akira345/Discrete-FM-Radio-Receiver-Project/Docs/FM_IF_5V/figures/ad3.png

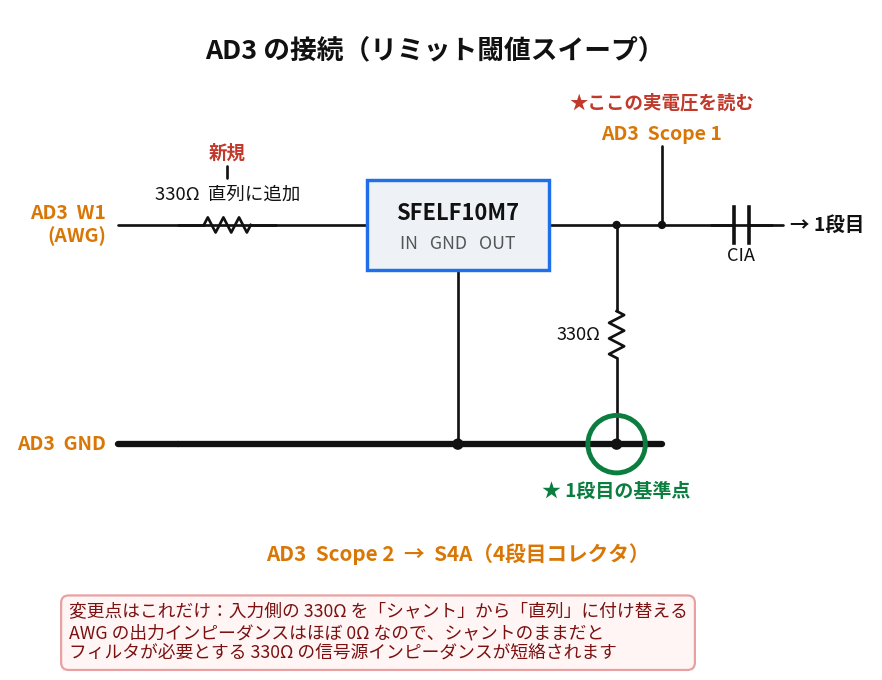
Docs/FM_IF_5V/figures/ad3.png
