akira345/Discrete-FM-Radio-Receiver-Project/Docs/FM_IF_5V/figures/chk_bias.png

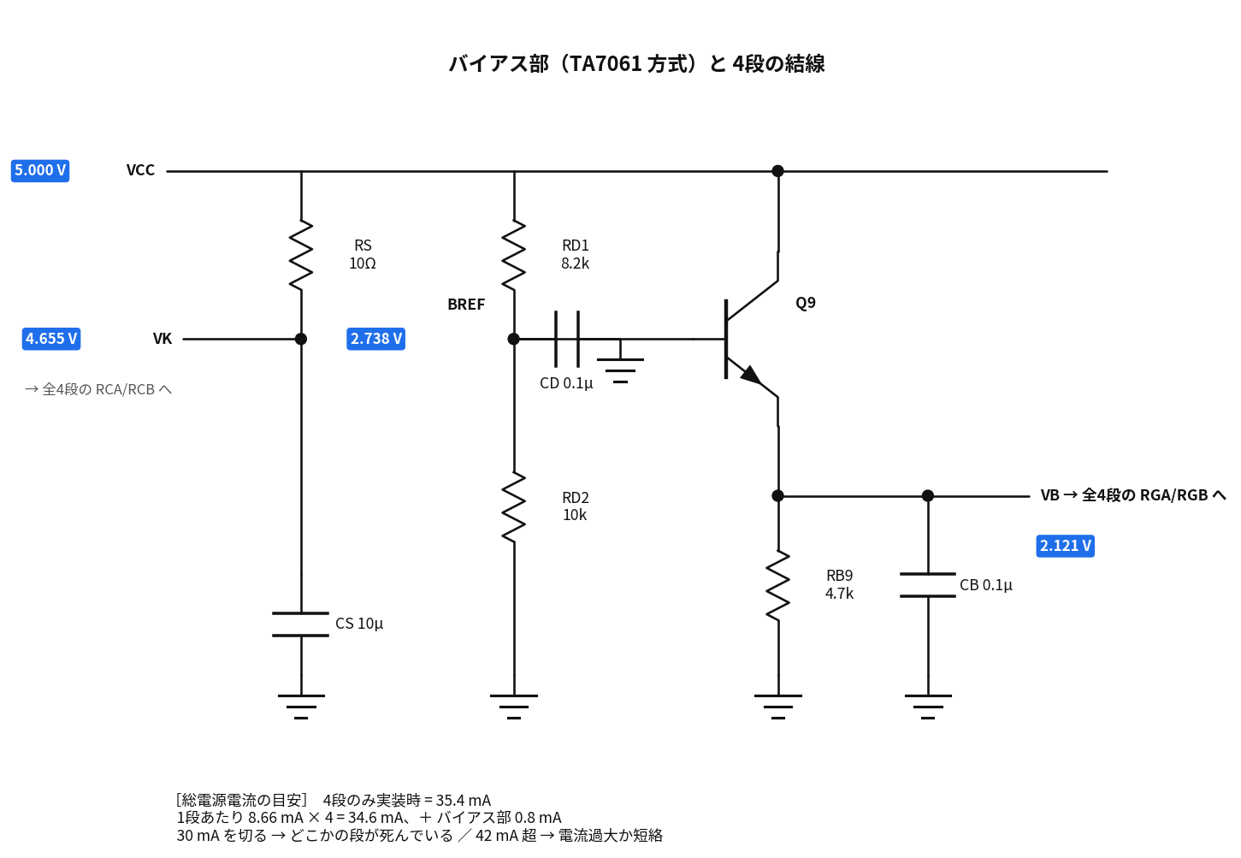
Docs/FM_IF_5V/figures/chk_bias.png
