akira345/Discrete-FM-Radio-Receiver-Project/Docs/FM_IF_5V/figures/gainshape.png

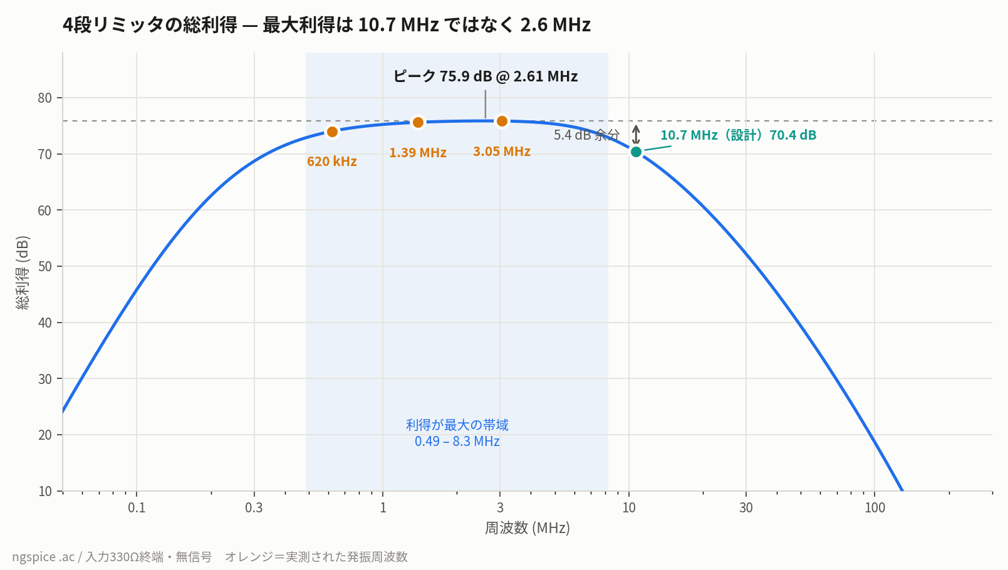
Docs/FM_IF_5V/figures/gainshape.png
