akira345/Discrete-FM-Radio-Receiver-Project/Docs/FM_IF_5V/figures/gndpath.png

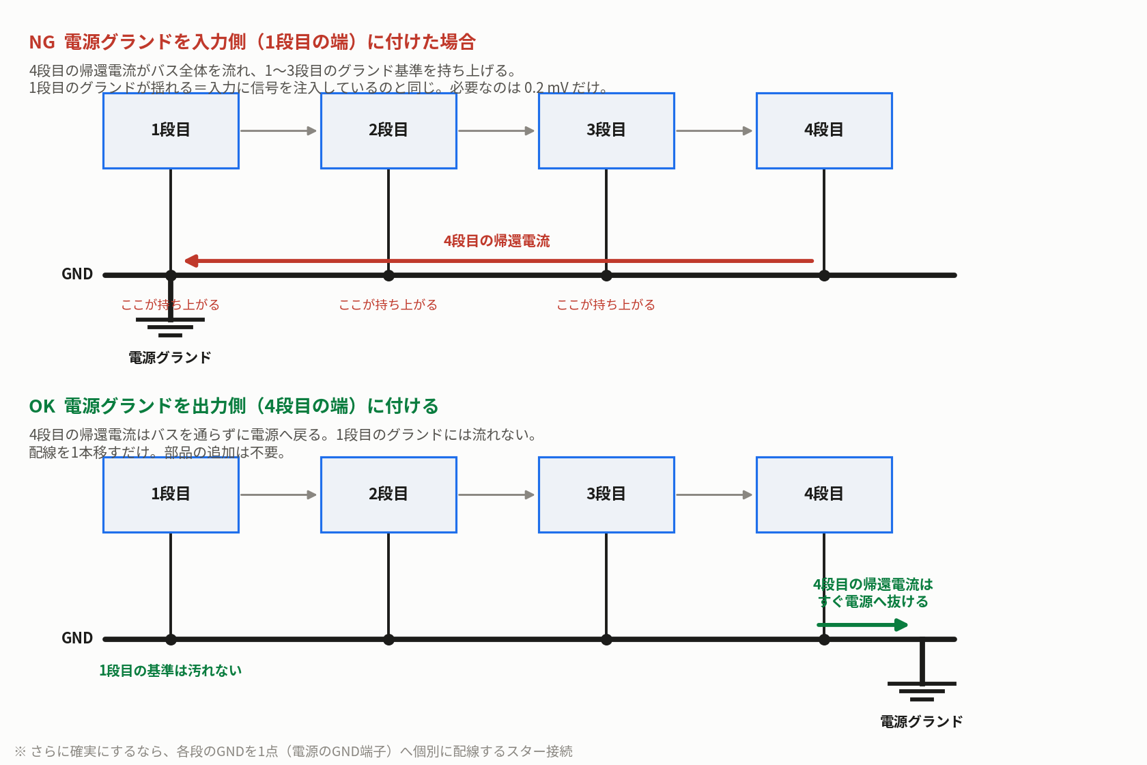
Docs/FM_IF_5V/figures/gndpath.png
