akira345/Discrete-FM-Radio-Receiver-Project/Docs/FM_IF_5V/figures/mpx_sync_block.png

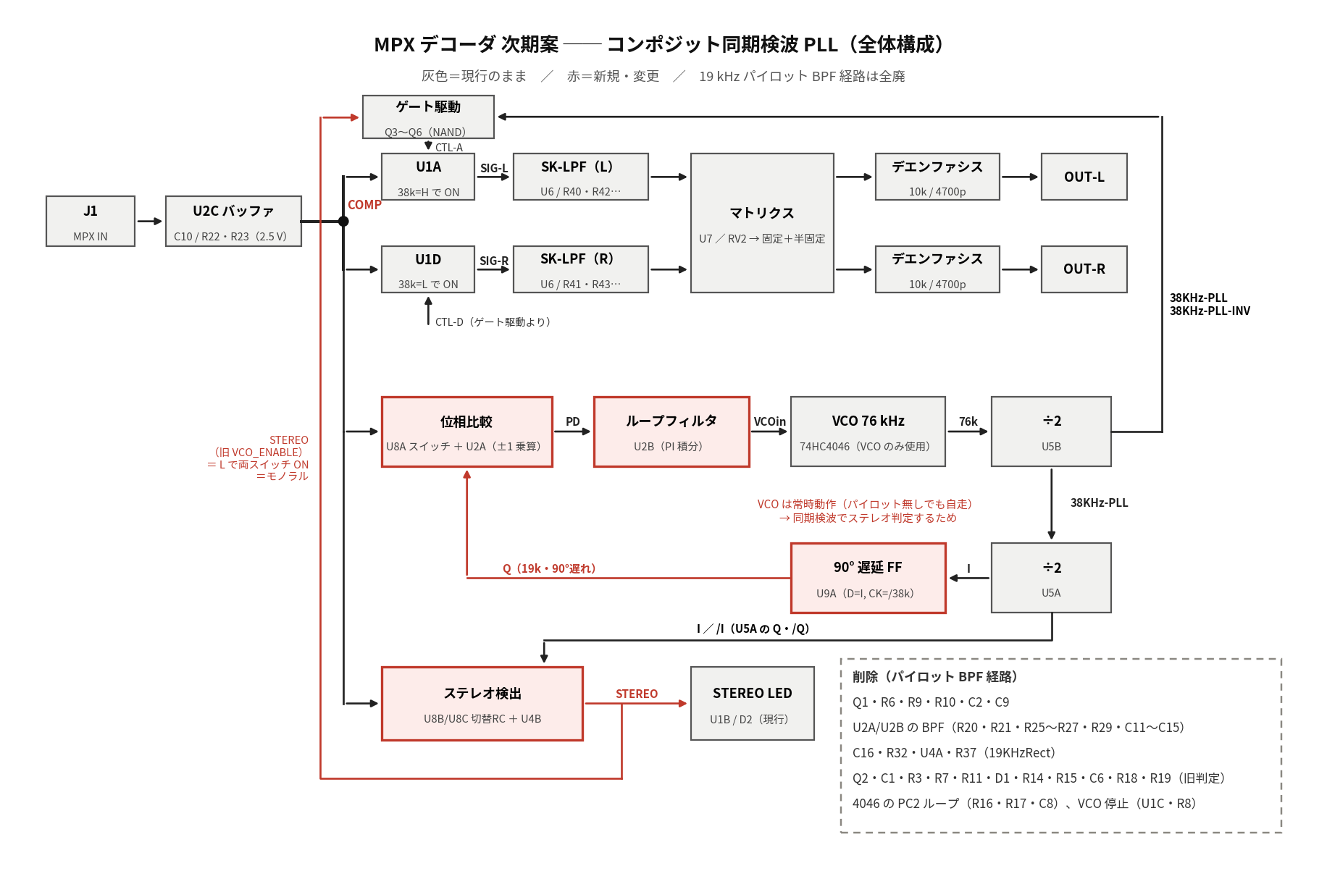
Docs/FM_IF_5V/figures/mpx_sync_block.png
