akira345/Discrete-FM-Radio-Receiver-Project/Docs/FM_IF_5V/figures/scurve.png

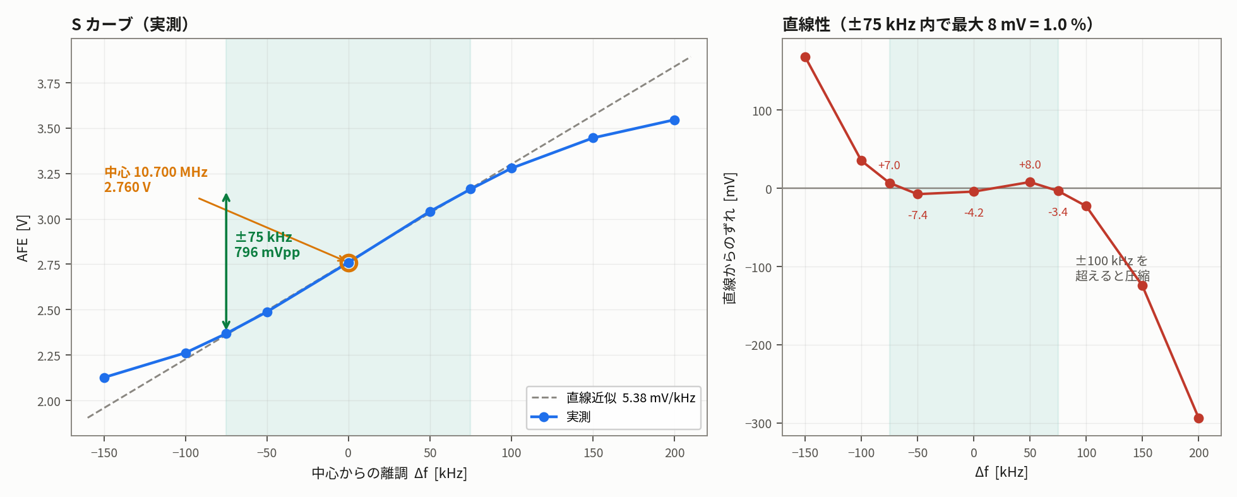
Docs/FM_IF_5V/figures/scurve.png
