akira345/Discrete-FM-Radio-Receiver-Project/Docs/FM_IF_5V/figures/sys_final.png

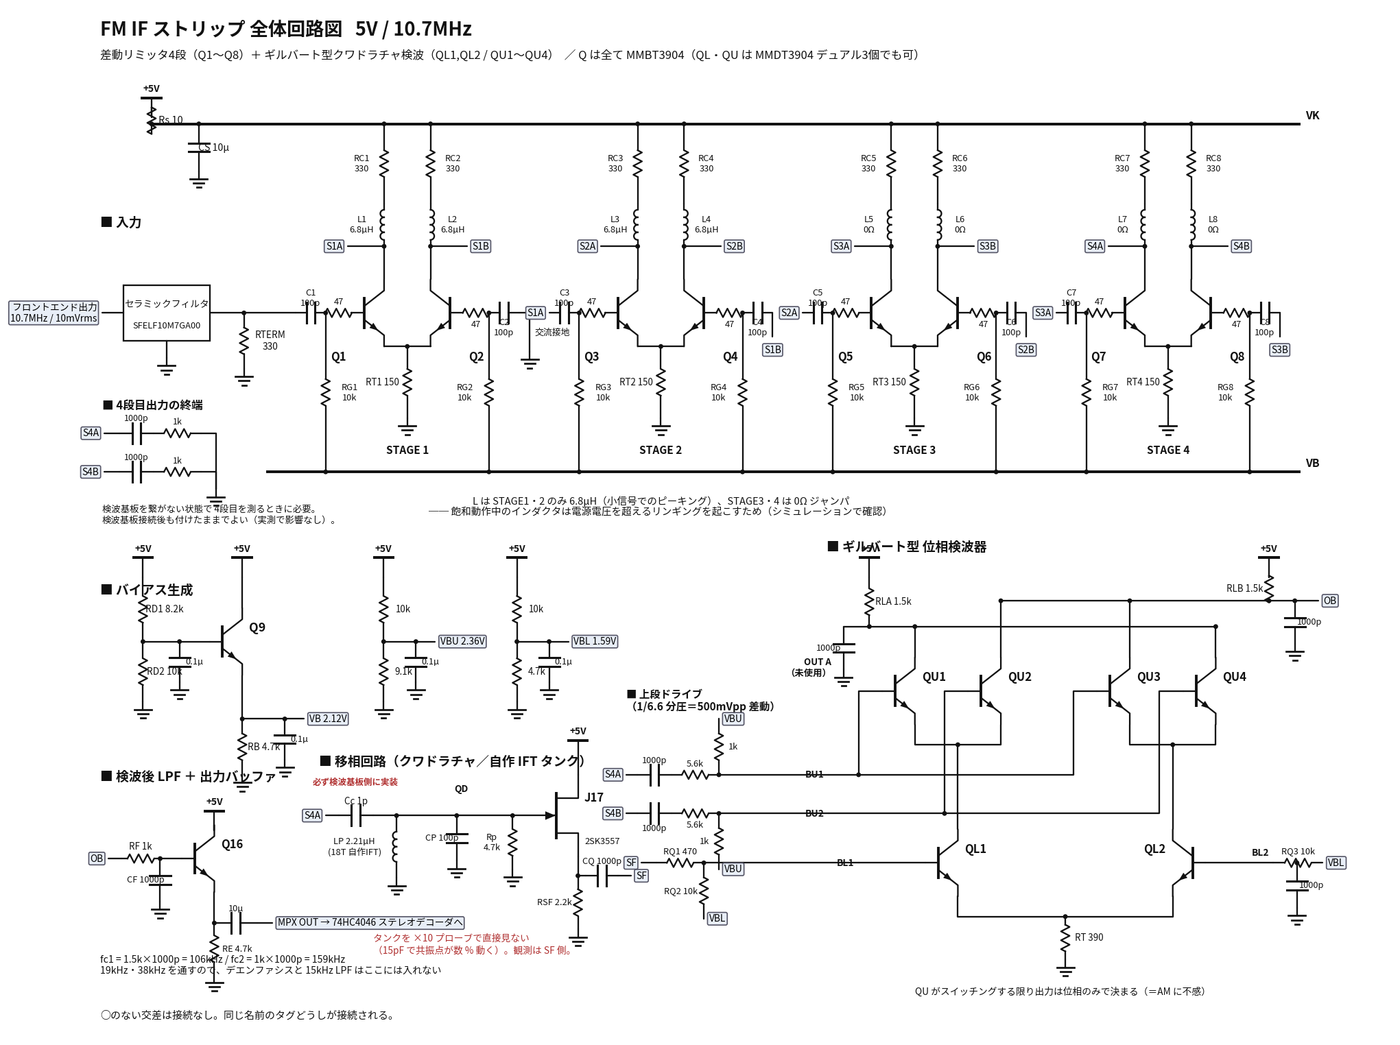
Docs/FM_IF_5V/figures/sys_final.png
