akira345/Discrete-FM-Radio-Receiver-Project/Docs/FM_IF_5V/reference/det_board.png

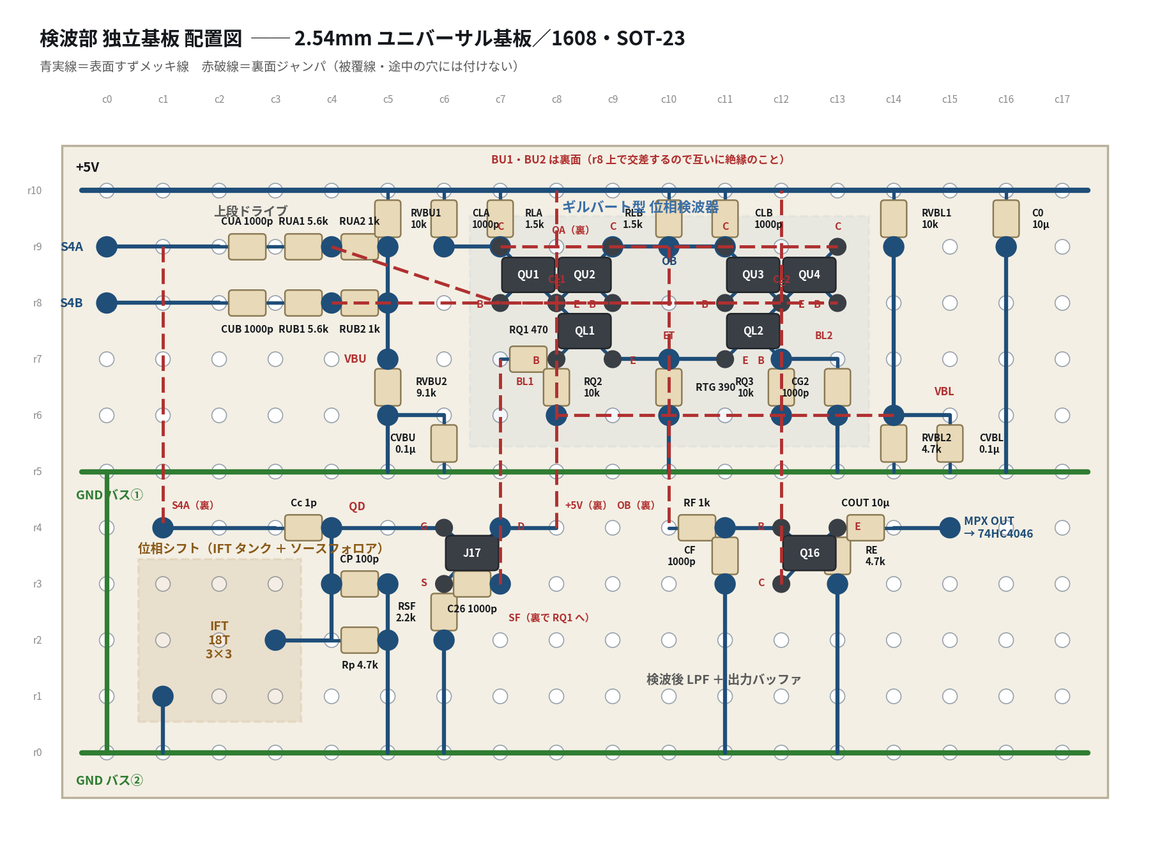
Docs/FM_IF_5V/reference/det_board.png
