akira345/Discrete-FM-Radio-Receiver-Project/Docs/FM_IF_5V/test_signals/mpx_L1k_check.png

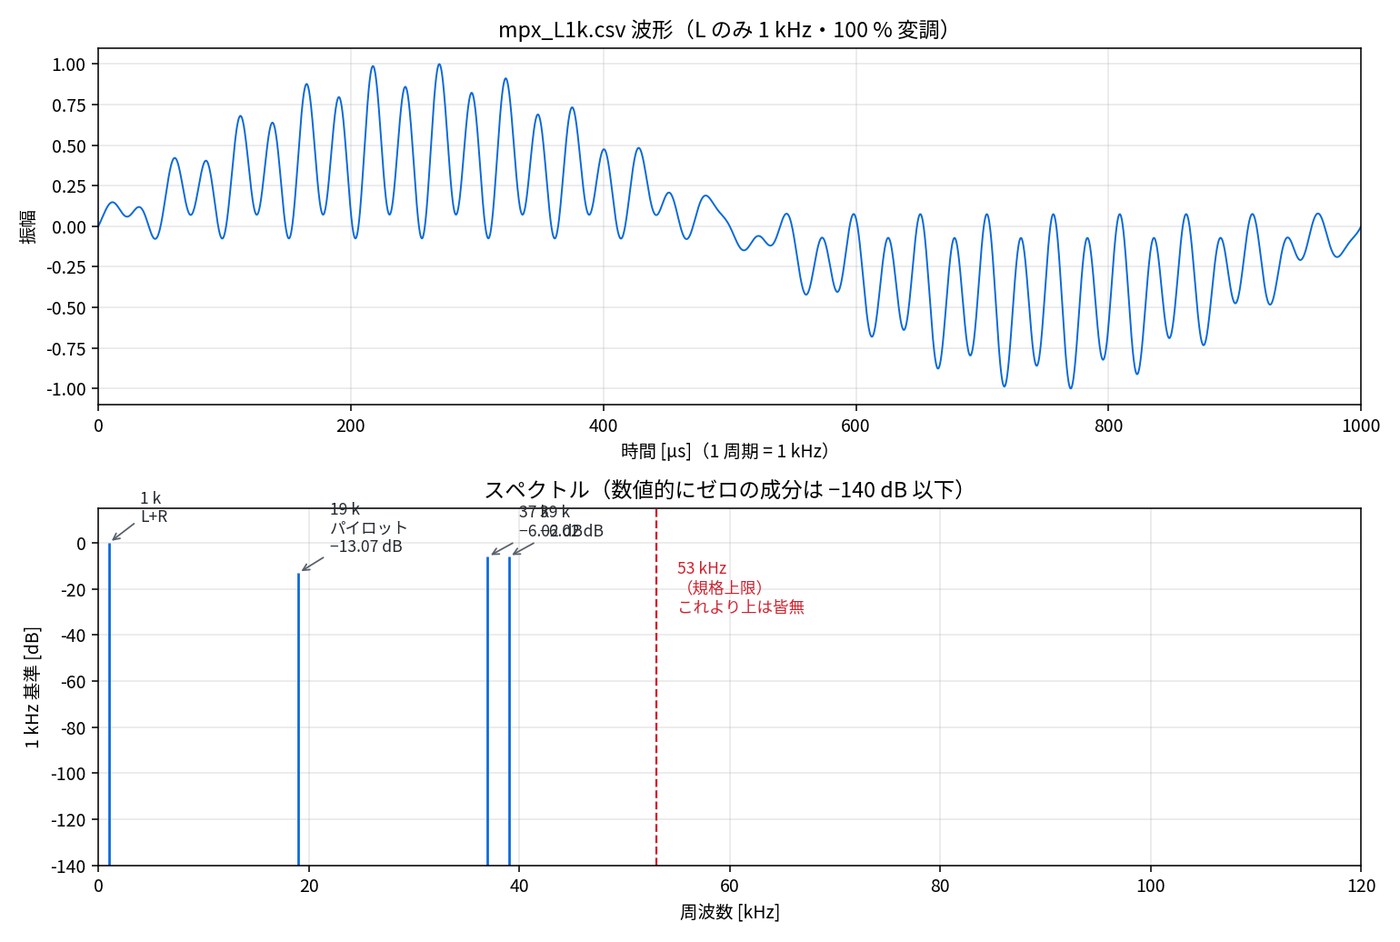
Docs/FM_IF_5V/test_signals/mpx_L1k_check.png
