akira345/Discrete-FM-Radio-Receiver-Project/Docs/FM_IF_5V/test_signals/preview_check.png

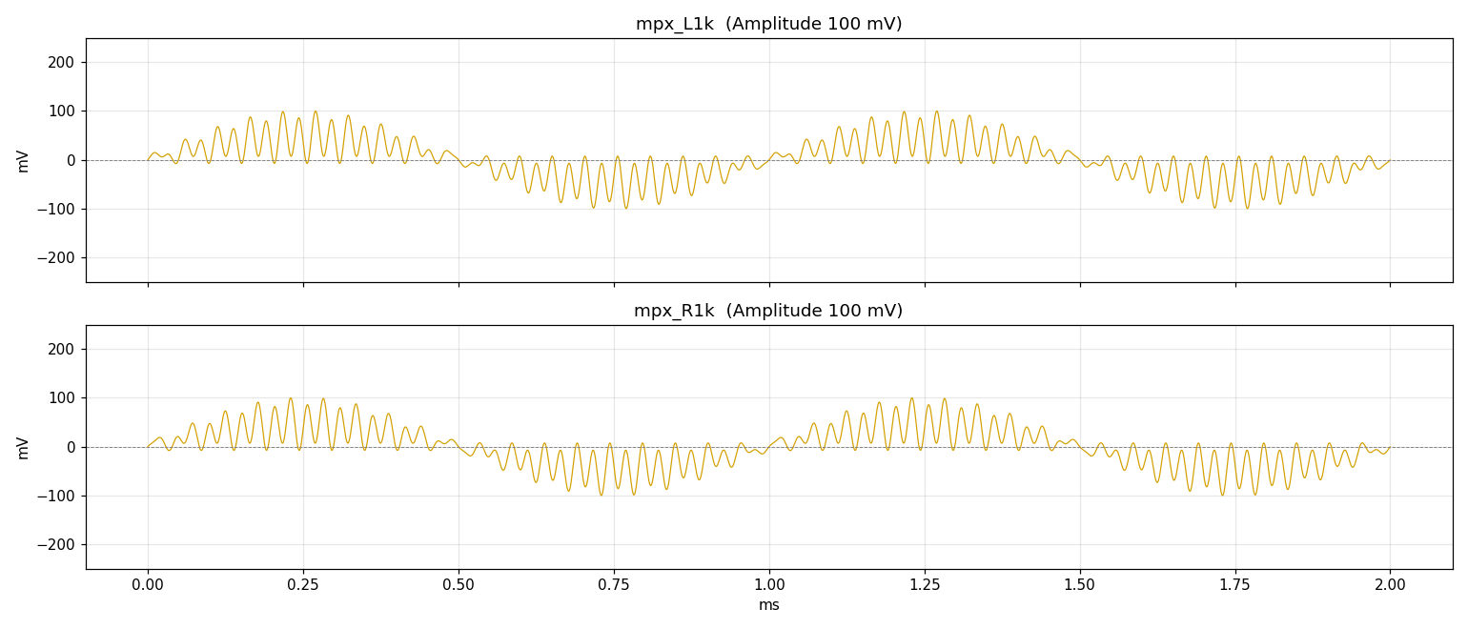
Docs/FM_IF_5V/test_signals/preview_check.png
