akira345/Discrete-FM-Radio-Receiver-Project/MPXDecorder-V4_SMD/MPXDecorder-V4_SMD.kicad_pcb

## KiCad design MPXDecorder-V4_SMD/MPXDecorder-V4_SMD.kicad_pcb (2026-10-10)

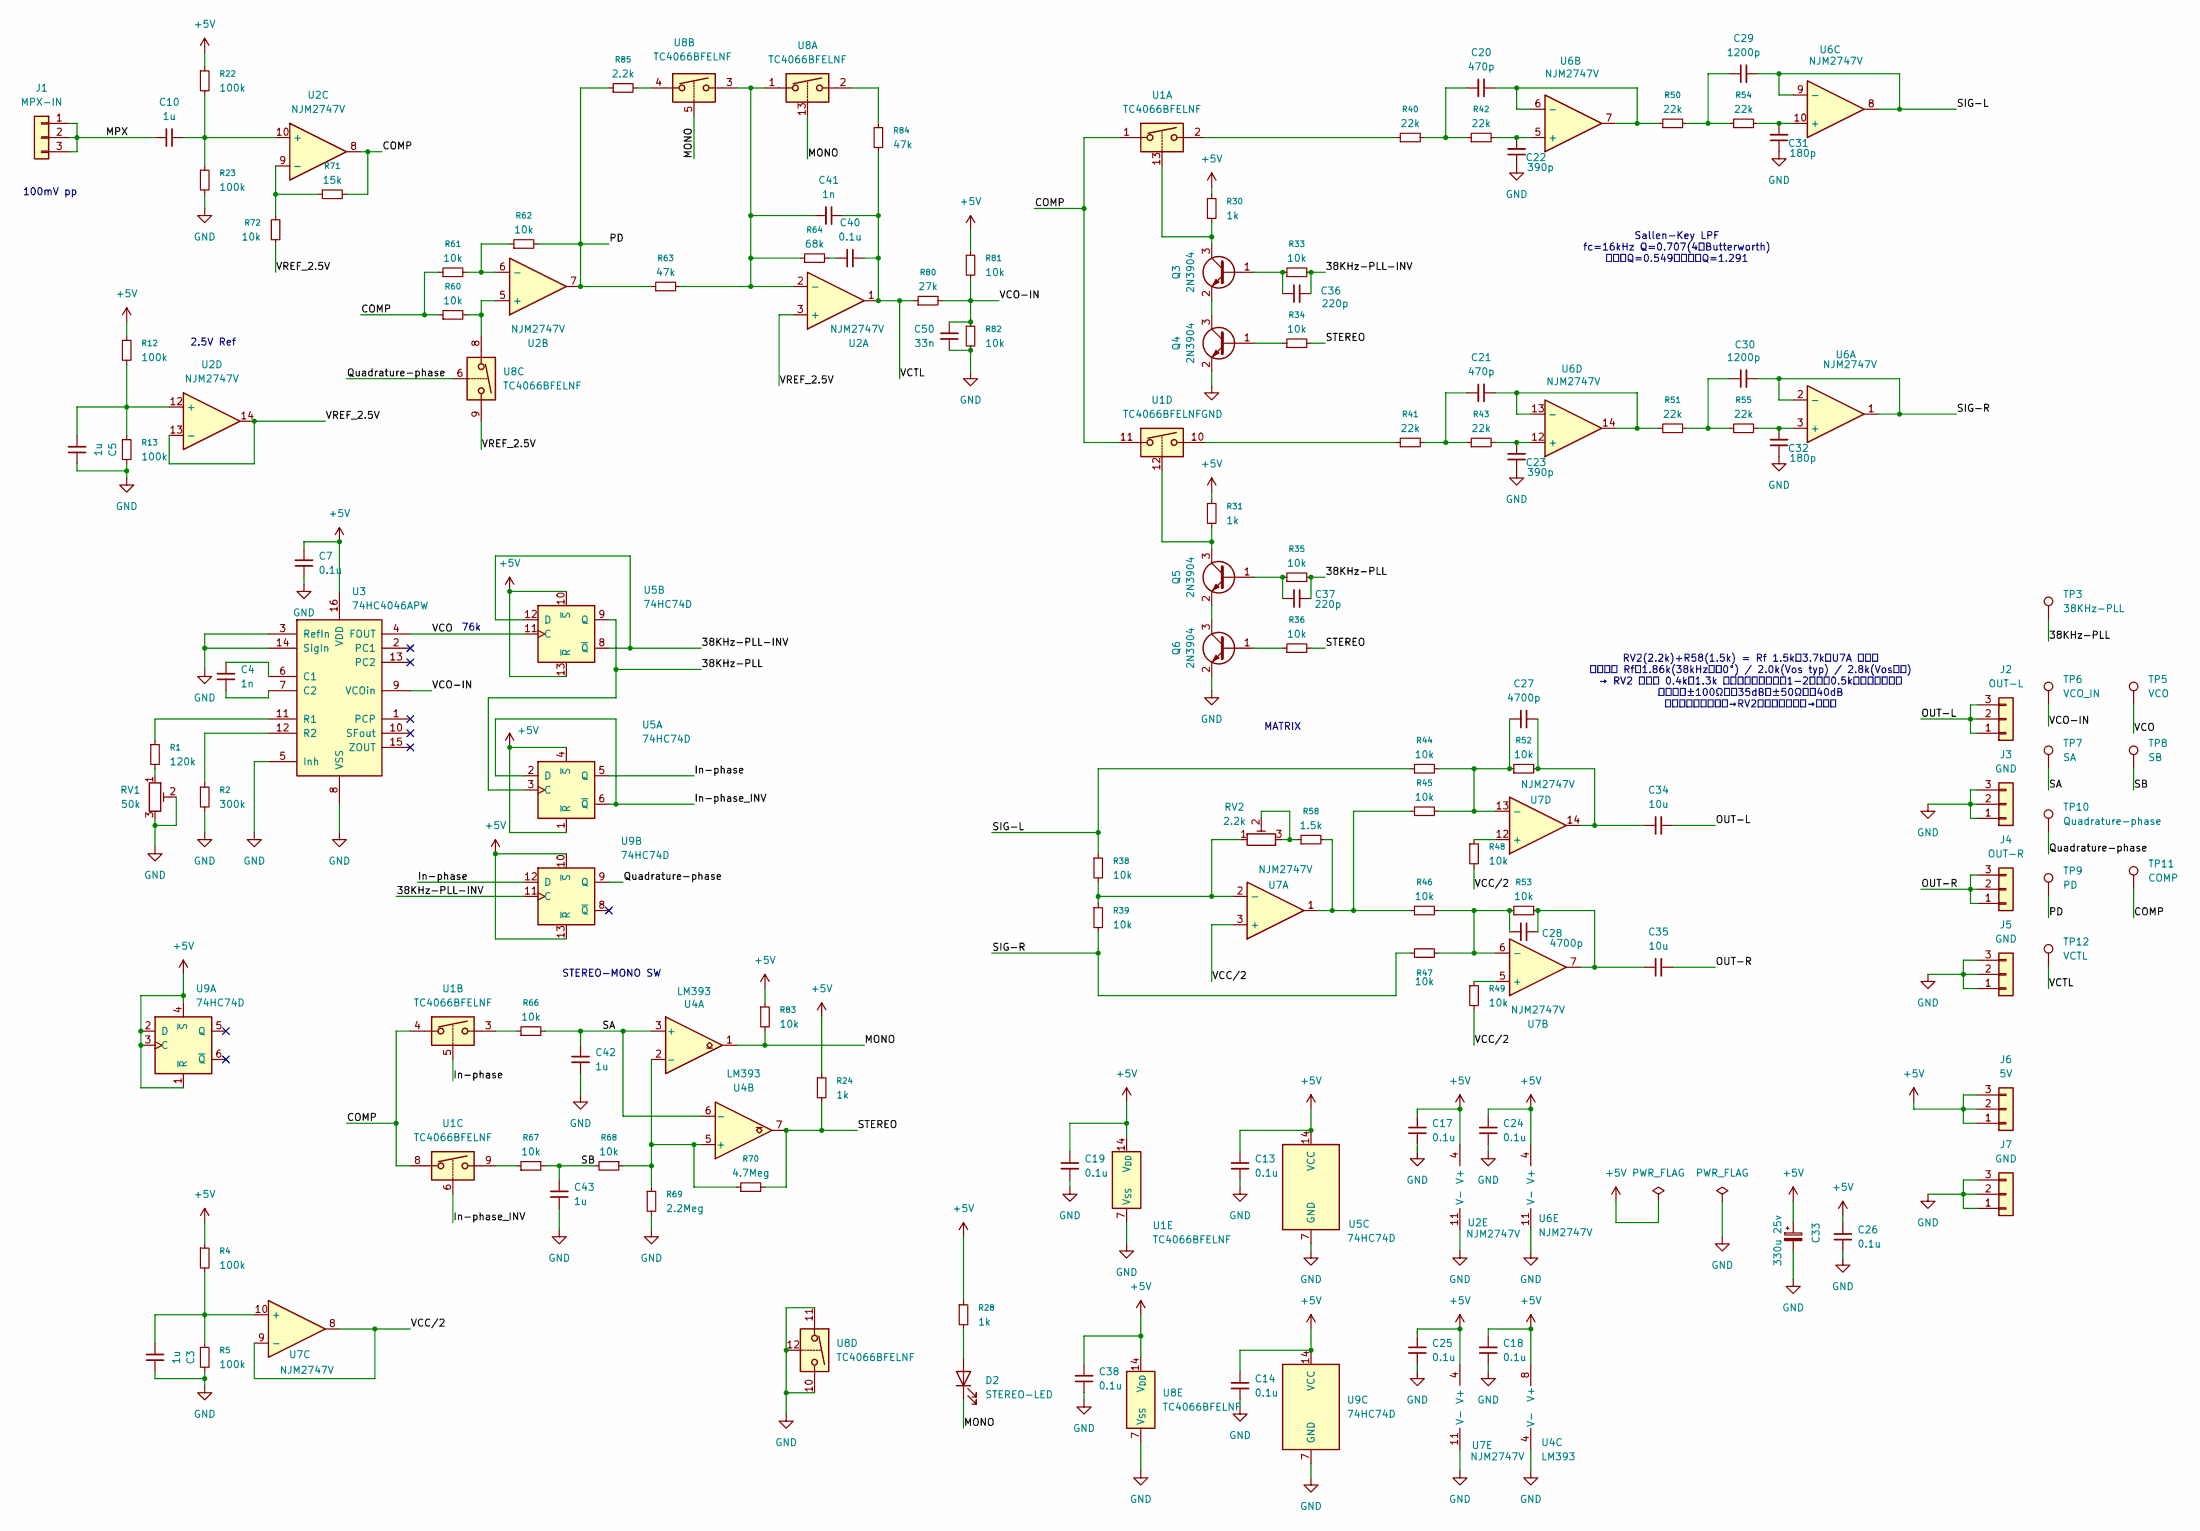
[picture p19: schematic MPXDecorder-V4_SMD.kicad_sch, FM MPX Decorder]

Parts:
C3, C5, C10, C42, C43: 1u; C_0603_1608Metric_Pad1.08x0.95mm_HandSolder
C4: 1n; C_0603_1608Metric_Pad1.08x0.95mm_HandSolder
C7, C13, C14, C17, C18, C19, C24, C25, C26, C38, C40: 0.1u; C_0603_1608Metric_Pad1.08x0.95mm_HandSolder
C20, C21: 470p; C_0603_1608Metric_Pad1.08x0.95mm_HandSolder
C22, C23: 390p; C_0603_1608Metric_Pad1.08x0.95mm_HandSolder
C27, C28: 4700p; C_0603_1608Metric_Pad1.08x0.95mm_HandSolder
C29, C30: 1200p; C_0603_1608Metric_Pad1.08x0.95mm_HandSolder
C31, C32: 180p; C_0603_1608Metric_Pad1.08x0.95mm_HandSolder
C33: 330u 25v; CP_Elec_10x10
C34, C35: 10u; C_1206_3216Metric_Pad1.33x1.80mm_HandSolder
C36, C37: 220p; C_0603_1608Metric_Pad1.08x0.95mm_HandSolder
C41: 1n; C_0805_2012Metric_Pad1.18x1.45mm_HandSolder
C50: 33n; C_1206_3216Metric_Pad1.33x1.80mm_HandSolder
D2: STEREO-LED; LED_0603_1608Metric_Pad1.05x0.95mm_HandSolder
J1: MPX-IN; PinHeader_1x03_P2.54mm_Vertical
J2: OUT-L; PinHeader_1x03_P2.54mm_Vertical
J3, J5, J7: GND; PinHeader_1x03_P2.54mm_Vertical
J4: OUT-R; PinHeader_1x03_P2.54mm_Vertical
J6: 5V; PinHeader_1x03_P2.54mm_Vertical
Q3, Q4, Q5, Q6: 2N3904; SOT-23_Handsoldering
R1: 120k; R_0603_1608Metric_Pad0.98x0.95mm_HandSolder
R2: 300k; R_0603_1608Metric_Pad0.98x0.95mm_HandSolder
R4, R5, R12, R13, R22, R23: 100k; R_0603_1608Metric_Pad0.98x0.95mm_HandSolder
R24, R28, R30, R31: 1k; R_0603_1608Metric_Pad0.98x0.95mm_HandSolder
R33, R34, R35, R36, R38, R39, R44, R45, R46, R47, R48, R49, R52, R53, R60, R61, R62, R66, R67, R68, R72, R81, R82, R83: 10k; R_0603_1608Metric_Pad0.98x0.95mm_HandSolder
R40, R41, R42, R43, R50, R51, R54, R55: 22k; R_0603_1608Metric_Pad0.98x0.95mm_HandSolder
R58: 1.5k; R_0603_1608Metric_Pad0.98x0.95mm_HandSolder
R63, R84: 47k; R_0603_1608Metric_Pad0.98x0.95mm_HandSolder
R64: 68k; R_0603_1608Metric_Pad0.98x0.95mm_HandSolder
R69: 2.2Meg; R_0603_1608Metric_Pad0.98x0.95mm_HandSolder
R70: 4.7Meg; R_0603_1608Metric_Pad0.98x0.95mm_HandSolder
R71: 15k; R_0603_1608Metric_Pad0.98x0.95mm_HandSolder
R80: 27k; R_0603_1608Metric_Pad0.98x0.95mm_HandSolder
R85: 2.2k; R_0603_1608Metric_Pad0.98x0.95mm_HandSolder
RV1: 50k; Potentiometer_Bourns_TC33X_Vertical
RV2: 2.2k; Potentiometer_Bourns_TC33X_Vertical
TP3: 38KHz-PLL; TestPoint_Pad_2.5x2.5mm
TP5: VCO; TestPoint_Pad_2.5x2.5mm
TP6: VCO_IN; TestPoint_Pad_2.5x2.5mm
TP7: SA; TestPoint_Pad_2.5x2.5mm
TP8: SB; TestPoint_Pad_2.5x2.5mm
TP9: PD; TestPoint_Pad_2.5x2.5mm
TP10: Quadrature-phase; TestPoint_Pad_2.5x2.5mm
TP11: COMP; TestPoint_Pad_2.5x2.5mm
TP12: VCTL; TestPoint_Pad_2.5x2.5mm
U1, U8: TC4066BFELNF; SO-14_5.3x10.2mm_P1.27mm
U2, U6, U7: NJM2747V; SSOP-14_5.3x6.2mm_P0.65mm
U3: 74HC4046APW; TSSOP-16_4.4x5mm_P0.65mm
U4: LM393; SOIC-8_3.9x4.9mm_P1.27mm
U5, U9: 74HC74D; SOIC-14_3.9x8.7mm_P1.27mm

Connections:
+5V: C7.1, C13.1, C14.1, C17.1, C18.1, C19.1, C24.1, C25.1, C26.1, C33.1, C38.1, J6.1, J6.2, J6.3, R4.1, R12.1, R22.1, R24.1, R28.1, R30.1, R31.1, R81.1, R83.1, U1.14 (V_{DD}), U2.4 (V+), U3.16 (VDD), U4.8 (V+), U5.1 (~R), U5.4 (~S), U5.10 (~S), U5.13 (~R), U5.14 (VCC), U6.4 (V+), U7.4 (V+), U8.14 (V_{DD}), U9.1 (~R), U9.2 (D), U9.3 (C), U9.4 (~S), U9.10 (~S), U9.13 (~R), U9.14 (VCC)
/38KHz-PLL: C37.2, R35.2, TP3.1 (1_1), U5.3 (C), U5.9 (Q)
/38KHz-PLL-INV: C36.2, R33.2, U5.8 (~Q), U5.12 (D), U9.11 (C)
/COMP: R60.1, R61.1, R71.2, TP11.1 (1_1), U1.1, U1.4, U1.8, U1.11, U2.8
/In-phase: U1.5, U5.5 (Q), U9.12 (D)
/In-phase_INV: U1.6, U5.2 (D), U5.6 (~Q)
/MONO: D2.1 (K), R83.2, U4.1, U8.5, U8.13
/MPX: C10.1, J1.1, J1.2, J1.3
/OUT-L: C34.2, J2.1, J2.2, J2.3
/OUT-R: C35.2, J4.1, J4.2, J4.3
/PD: R62.2, R63.1, R85.1, TP9.1 (1_1), U2.7
/Quadrature-phase: TP10.1 (1_1), U8.6, U9.9 (Q)
/SA: C42.1, R66.2, TP7.1 (1_1), U4.3 (+), U4.6 (-)
/SB: C43.1, R67.2, R68.2, TP8.1 (1_1)
/SIG-L: C29.2, R38.1, R44.1, U6.8, U6.9 (-)
/SIG-R: C30.2, R39.2, R47.1, U6.1, U6.2 (-)
/STEREO: R24.2, R34.2, R36.2, R70.2, U4.7
/VCC/2: R48.2, R49.2, U7.3 (+), U7.8, U7.9 (-)
/VCO: TP5.1 (1_1), U3.4 (FOUT), U5.11 (C)
/VCO-IN: C50.1, R80.2, R81.2, R82.1, TP6.1 (1_1), U3.9 (VCOin)
/VCTL: C40.2, C41.2, R80.1, R84.1, TP12.1 (1_1), U2.1
/VREF_2.5V: R72.1, U2.3 (+), U2.13 (-), U2.14, U8.9
GND: C3.2, C5.2, C7.2, C13.2, C14.2, C17.2, C18.2, C19.2, C22.1, C23.1, C24.2, C25.2, C26.2, C31.1, C32.1, C33.2, C38.2, C42.2, C43.2, C50.2, J3.1, J3.2, J3.3, J5.1, J5.2, J5.3, J7.1, J7.2, J7.3, Q4.2 (E), Q6.2 (E), R2.2, R5.2, R13.2, R23.2, R69.2, R82.2, RV1.2, RV1.3, U1.7 (V_{SS}), U2.11 (V-), U3.3 (RefIn), U3.5 (Inh), U3.8 (VSS), U3.14 (SigIn), U4.4 (V-), U5.7 (GND), U6.11 (V-), U7.11 (V-), U8.7 (V_{SS}), U8.10, U8.11, U8.12, U9.7 (GND)
unnamed: C20.1, R40.2, R42.1
unnamed: C21.1, R41.2, R43.1
unnamed: C27.2, C34.1, R52.2, U7.14
unnamed: C28.2, C35.1, R53.2, U7.7
unnamed: C29.1, R50.2, R54.1
unnamed: C30.1, R51.2, R55.1
unnamed: C40.1, R64.2
unnamed: D2.2 (A), R28.2
unnamed: C36.1, Q3.1 (B), R33.1
unnamed: Q3.3 (C), R30.2, U1.13
unnamed: Q3.2 (E), Q4.3 (C)
unnamed: Q4.1 (B), R34.1
unnamed: C37.1, Q5.1 (B), R35.1
unnamed: Q5.3 (C), R31.2, U1.12
unnamed: Q5.2 (E), Q6.3 (C)
unnamed: Q6.1 (B), R36.1
unnamed: R1.2, RV1.1
unnamed: R40.1, U1.2
unnamed: R41.1, U1.10
unnamed: R45.1, R46.1, R58.2, U7.1
unnamed: R58.1, RV2.2, RV2.3
unnamed: R66.1, U1.3
unnamed: R67.1, U1.9
unnamed: R84.2, U8.2
unnamed: R85.2, U8.4
unnamed: C41.1, R63.2, R64.1, U2.2 (-), U8.1, U8.3
unnamed: R60.2, U2.5 (+), U8.8
unnamed: R61.2, R62.1, U2.6 (-)
unnamed: C10.2, R22.2, R23.1, U2.10 (+)
unnamed: R71.1, R72.2, U2.9 (-)
unnamed: C5.1, R12.2, R13.1, U2.12 (+)
unnamed: C4.1, U3.6 (C1)
unnamed: C4.2, U3.7 (C2)
unnamed: R1.1, U3.11 (R1)
unnamed: R2.1, U3.12 (R2)
unnamed: R68.1, R69.1, R70.1, U4.2 (-), U4.5 (+)
unnamed: C32.2, R55.2, U6.3 (+)
unnamed: C22.2, R42.2, U6.5 (+)
unnamed: C20.2, R50.1, U6.6 (-), U6.7
unnamed: C31.2, R54.2, U6.10 (+)
unnamed: C23.2, R43.2, U6.12 (+)
unnamed: C21.2, R51.1, U6.13 (-), U6.14
unnamed: R38.2, R39.1, RV2.1, U7.2 (-)
unnamed: R49.1, U7.5 (+)
unnamed: C28.1, R46.2, R47.2, R53.1, U7.6 (-)
unnamed: C3.1, R4.2, R5.1, U7.10 (+)
unnamed: R48.1, U7.12 (+)
unnamed: C27.1, R44.2, R45.2, R52.1, U7.13 (-)

Notes on the sheet:
RV2(2.2k)+R58(1.5k) = Rf 1.5k〜3.7k（U7A 帰還） 予測最適 Rf：1.86k(38kHz誤差0°) / 2.0k(Vos typ) / 2.8k(Vos最悪) → RV2 単体で 0.4k〜1.3k 付近。実装前にピン1-2間を約0.5kに合わせておく 許容幅：±100Ωで約35dB、±50Ωで約40dB 漏れが主信号と同相→RV2を大きく、逆相→小さく
76k
Sallen-Key LPF fc=16kHz Q=0.707(4次Butterworth) 前段：Q=0.549 後段：Q=1.291
2.5V Ref
STEREO-MONO SW
100mV pp
MATRIX

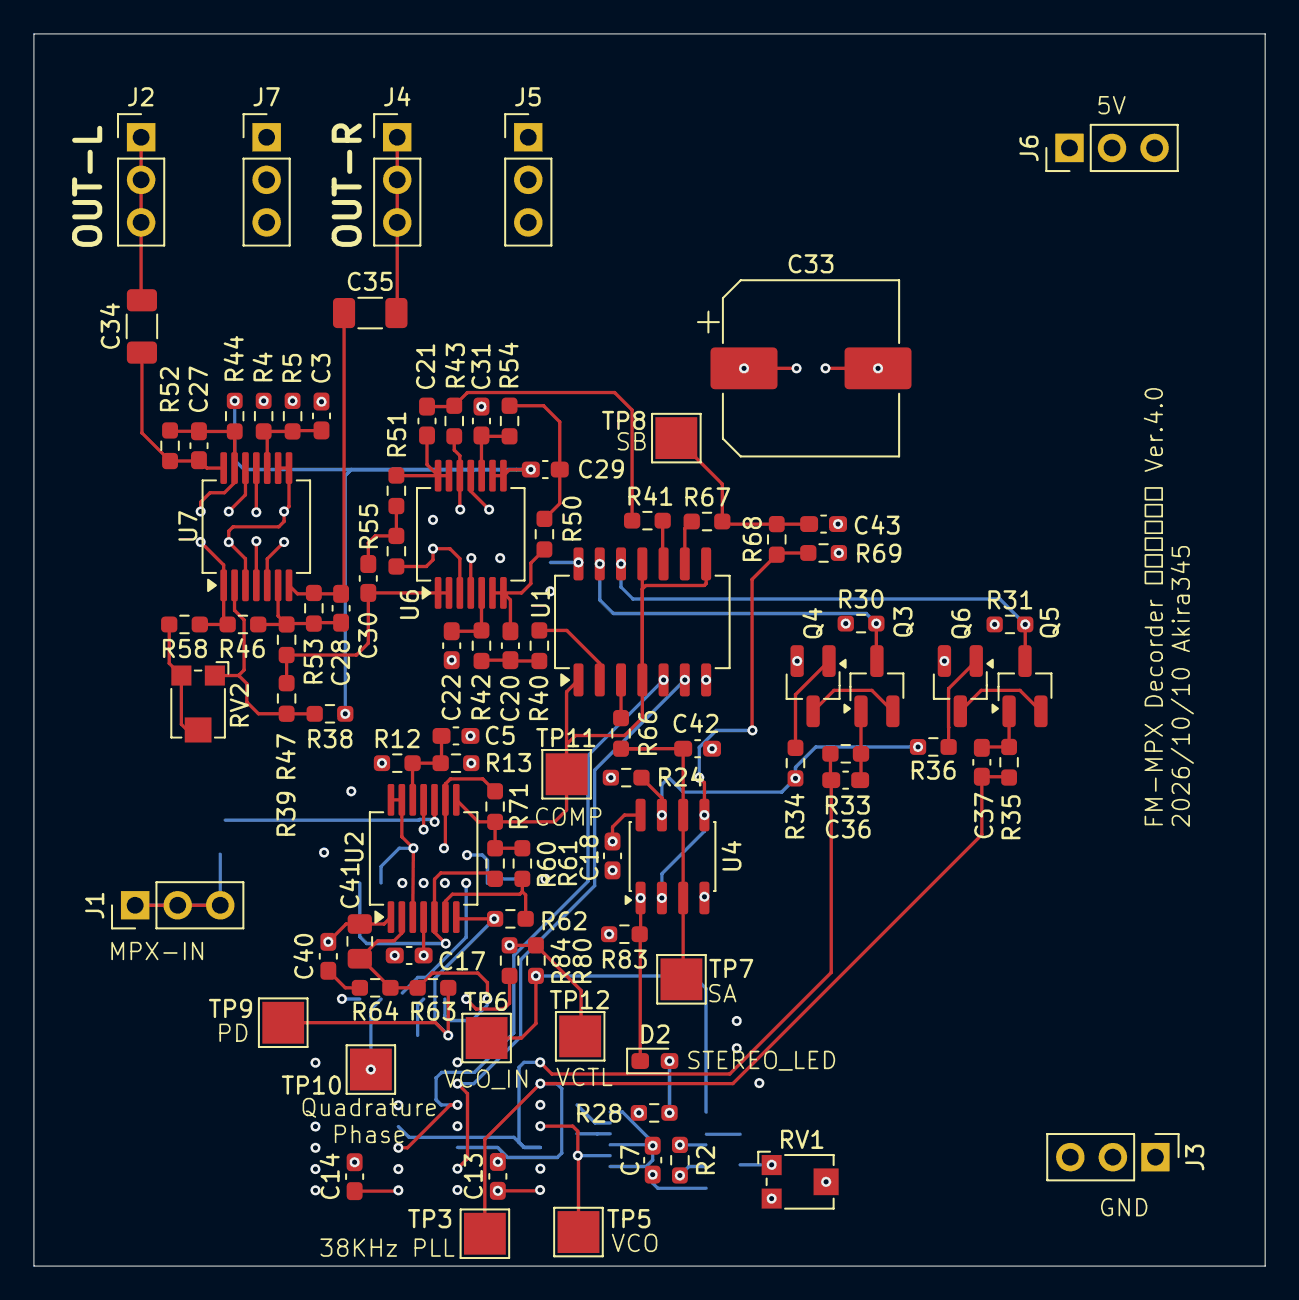
[picture p20: board MPXDecorder-V4_SMD.kicad_pcb from above]

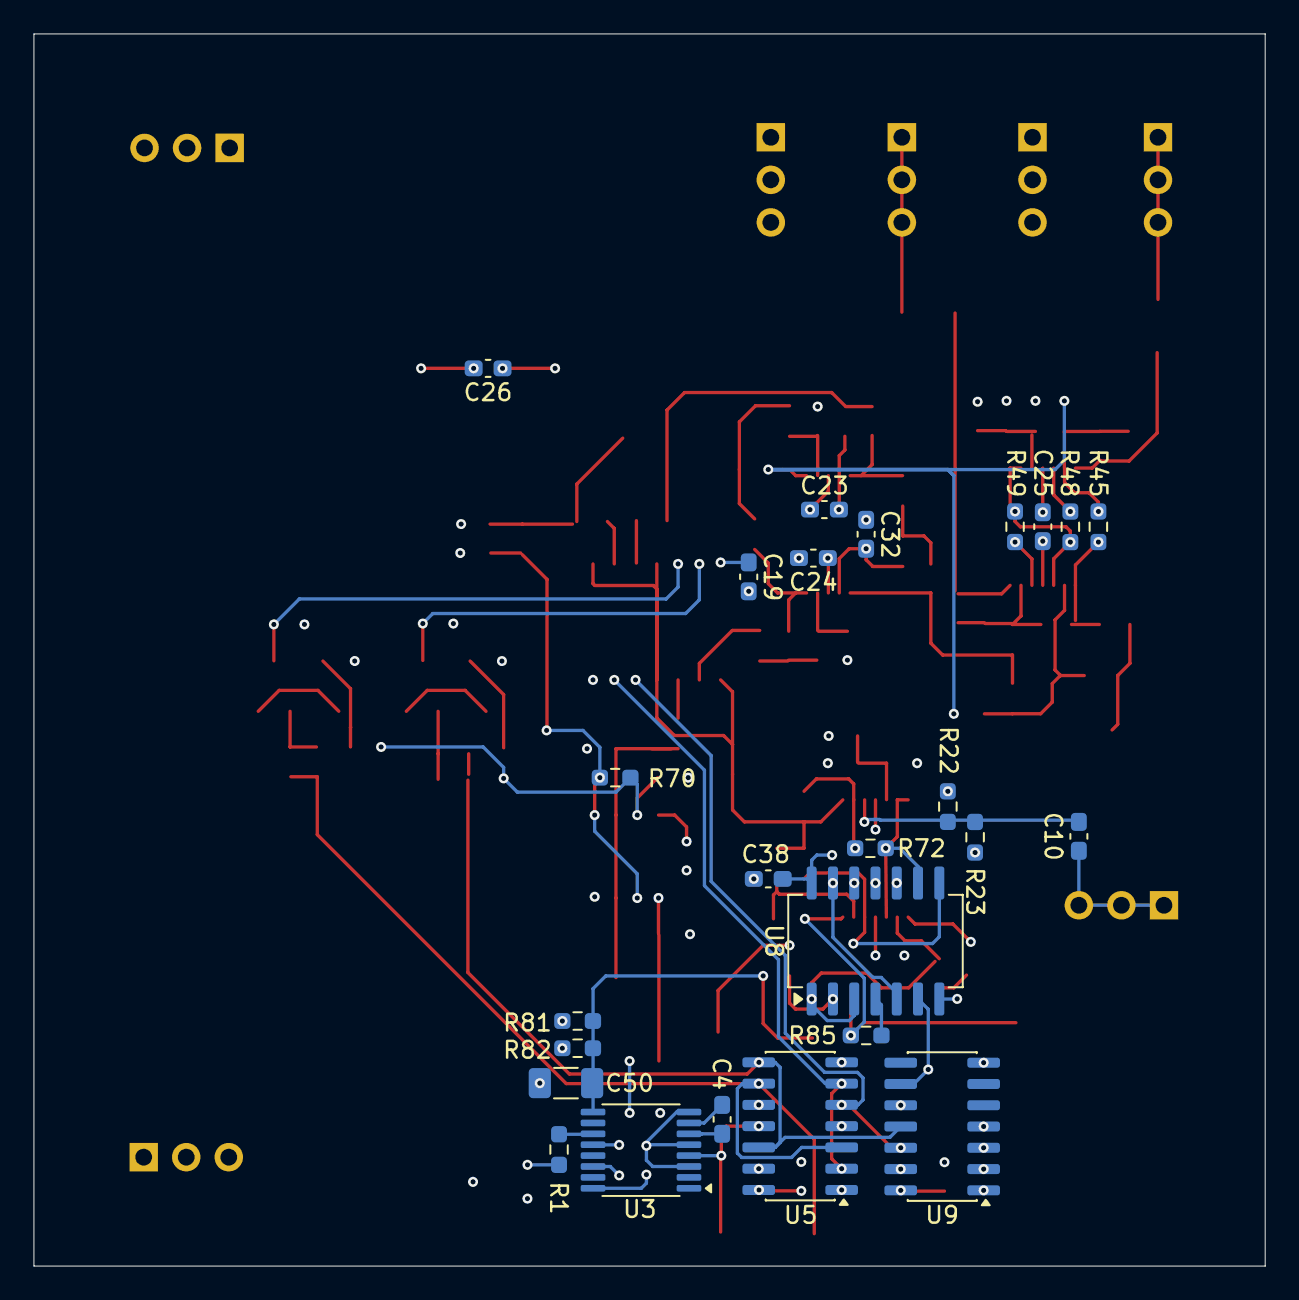
[picture p21: board MPXDecorder-V4_SMD.kicad_pcb from below]

Board: 4 copper layers, 73.5 x 73.6 mm, 119 parts (25 on the bottom side), 71 nets.
