akira345/Discrete-FM-Radio-Receiver-Project/MPXDecorder/MPXDecorder.kicad_pcb

## KiCad design MPXDecorder/MPXDecorder.kicad_pcb (2026-10-04)

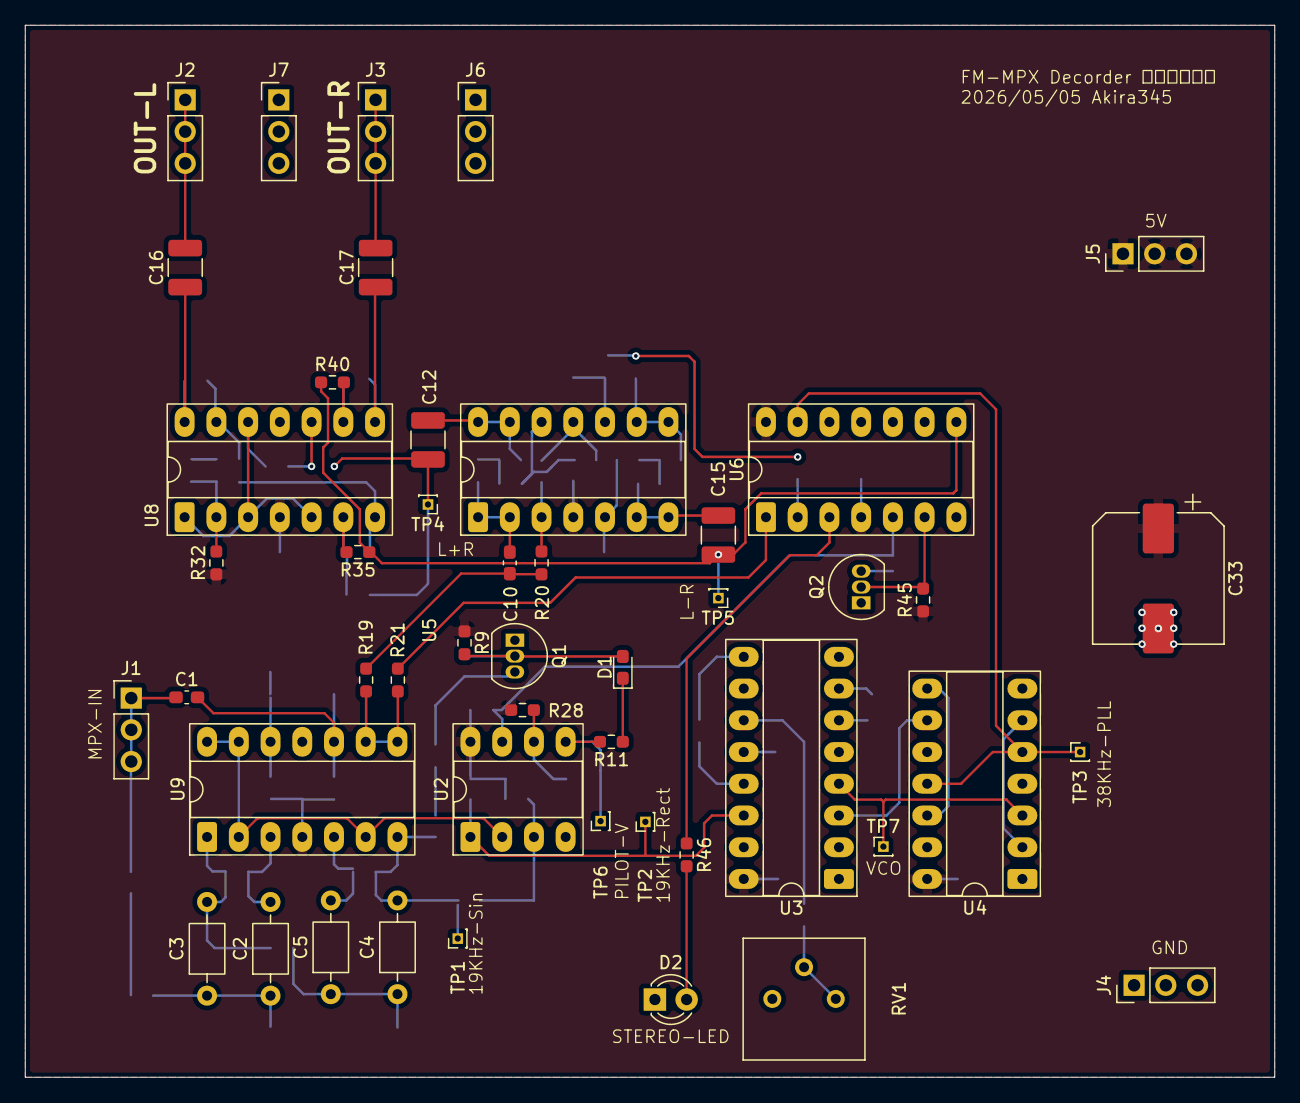
[picture p22: board MPXDecorder.kicad_pcb from above]

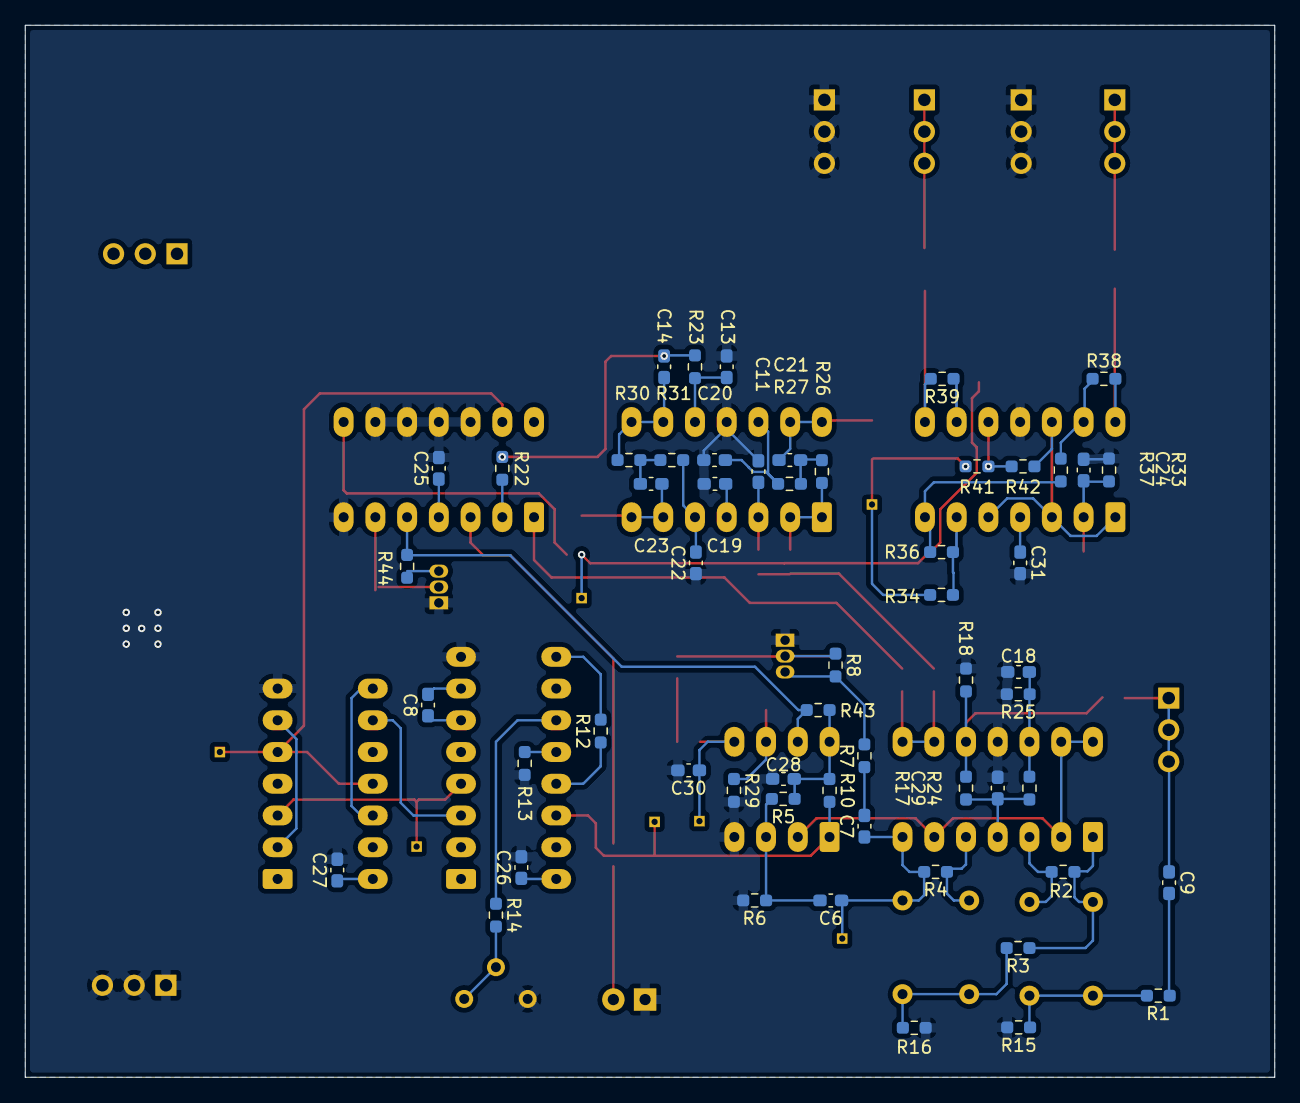
[picture p23: board MPXDecorder.kicad_pcb from below]

Board: 2 copper layers, 100.0 x 84.2 mm, 104 parts (56 on the bottom side), 66 nets.

Parts:
C1, C18, C24, C30: 1u; C_0603_1608Metric_Pad1.08x0.95mm_HandSolder
C2, C3, C4, C5: 0.01u; C_Axial_L3.8mm_D2.6mm_P7.50mm_Horizontal
C6, C7, C9, C19, C25, C26, C27, C28, C29, C31: 0.1u; C_0603_1608Metric_Pad1.08x0.95mm_HandSolder
C8: 1n; C_0603_1608Metric_Pad1.08x0.95mm_HandSolder
C10, C11, C13, C14, C20, C21, C22, C23: 3.3n; C_0603_1608Metric_Pad1.08x0.95mm_HandSolder
C12, C15, C16, C17: 10u; C_1210_3225Metric_Pad1.33x2.70mm_HandSolder
C33: 330u 25v; CP_Elec_10x10
D1: 1s1588; D_0603_1608Metric_Pad1.05x0.95mm_HandSolder
D2: STEREO-LED; LED_D3.0mm
J1: MPX-IN; PinHeader_1x03_P2.54mm_Vertical
J2: OUT-L; PinHeader_1x03_P2.54mm_Vertical
J3: OUT-R; PinHeader_1x03_P2.54mm_Vertical
J4, J6, J7: GND; PinHeader_1x03_P2.54mm_Vertical
J5: 5V; PinHeader_1x03_P2.54mm_Vertical
Q1, Q2: 2SC1815; TO-92_Inline
R1, R3: 7.5k; R_0603_1608Metric_Pad0.98x0.95mm_HandSolder
R2, R4: 15k; R_0603_1608Metric_Pad0.98x0.95mm_HandSolder
R5, R6, R13, R17, R18, R24, R25, R32, R33: 100k; R_0603_1608Metric_Pad0.98x0.95mm_HandSolder
R7, R9, R10, R21, R43, R44, R45: 10k; R_0603_1608Metric_Pad0.98x0.95mm_HandSolder
R8: 20k; R_0603_1608Metric_Pad0.98x0.95mm_HandSolder
R11, R46: 1k; R_0603_1608Metric_Pad0.98x0.95mm_HandSolder
R12, R14: 4.7k; R_0603_1608Metric_Pad0.98x0.95mm_HandSolder
R15, R16: 39; R_0603_1608Metric_Pad0.98x0.95mm_HandSolder
R19, R20, R22, R23, R26, R27, R30, R31: 3.3k; R_0603_1608Metric_Pad0.98x0.95mm_HandSolder
R28: 5.1k; R_0603_1608Metric_Pad0.98x0.95mm_HandSolder
R29: 1.6k; R_0603_1608Metric_Pad0.98x0.95mm_HandSolder
R34, R35, R36, R37, R38, R39, R40, R41, R42: 47k; R_0603_1608Metric_Pad0.98x0.95mm_HandSolder
RV1: 2k; Potentiometer_Bourns_3386P_Vertical
TP1: 19KHz-Sin; PinHeader_1x01_P1.00mm_Vertical
TP2: 19KHz-Rect; PinHeader_1x01_P1.00mm_Vertical
TP3: 38KHz-PLL; PinHeader_1x01_P1.00mm_Vertical
TP4: L+R; PinHeader_1x01_P1.00mm_Vertical
TP5: L-R; PinHeader_1x01_P1.00mm_Vertical
TP6: PILOT-V; PinHeader_1x01_P1.00mm_Vertical
TP7: VCO; PinHeader_1x01_P1.00mm_Vertical
U2: LM393; DIP-8_W7.62mm_Socket_LongPads
U3: 4046; DIP-16_W7.62mm_Socket_LongPads
U4: 74HC74; DIP-14_W7.62mm_Socket_LongPads
U5, U8, U9: HA17902; DIP-14_W7.62mm_Socket_LongPads
U6: CD4066BE; DIP-14_W7.62mm_Socket_LongPads

Connections:
+5V: C19.1, C25.1, C26.1, C27.1, C28.1, C29.1, C31.1, C33.1, J5.1, J5.2, J5.3, R5.1, R9.1, R10.1, R17.1, R24.1, R28.1, R32.1, R43.1, R45.1, U2.8 (V+), U3.16 (VDD), U4.14 (VCC), U5.4 (V+), U6.4, U6.14 (V_{DD}), U8.4 (V+), U9.4 (V+)
/19KHzRect: R10.2, TP2.1 (1_1), U2.1, U3.14 (SigIn)
/19KHzSin: C4.2, C6.1, C7.1, R4.2, TP1.1 (1_1), U9.7
/38KHz-PLL: TP3.1 (1_1), U4.5 (Q), U4.11 (C), U6.13
/L+R: C12.2, R34.1, R41.1, TP4.1 (1_1)
/L-R: C15.2, R35.1, R40.1, TP5.1 (1_1), U6.8
/MPX: C1.1, C9.1, J1.1, J1.2, J1.3
/OUT-L: C16.2, J2.1, J2.2, J2.3
/OUT-R: C17.2, J3.1, J3.2, J3.3
/PILOT-V: C30.1, R11.2, TP6.1 (1_1), U2.5 (+)
/VCO: TP7.1 (1_1), U3.4 (FOUT), U4.3 (C)
GND: C11.1, C13.1, C18.2, C19.2, C20.1, C22.1, C24.2, C25.2, C26.2, C27.2, C28.2, C29.2, C30.2, C31.2, C33.2, D2.1 (K), J4.1, J4.2, J4.3, J6.1, J6.2, J6.3, J7.1, J7.2, J7.3, Q1.1 (E), Q2.1 (E), R6.2, R13.2, R15.2, R16.2, R18.2, R25.2, R29.2, R33.2, RV1.3, U2.4 (V-), U3.8 (VSS), U4.7 (GND), U5.11 (V-), U6.7 (V_{SS}), U6.9, U6.10, U6.11, U6.12, U8.11 (V-), U9.11 (V-)
unnamed: C2.1, C3.1, R1.2, R15.1
unnamed: C3.2, R2.2, R3.1, U9.1
unnamed: C4.1, C5.1, R3.2, R16.1
unnamed: C7.2, R7.1
unnamed: C9.2, R1.1
unnamed: C10.1, R19.2, R20.1
unnamed: C14.1, R22.2, R23.1
unnamed: C16.1, R38.2, U8.14
unnamed: C17.1, R39.2, U8.8
unnamed: C21.1, R26.2, R27.1
unnamed: C23.1, R30.2, R31.1
unnamed: D1.2 (A), Q1.2 (C), R8.1, R9.2
unnamed: D1.1 (K), R11.1
unnamed: D2.2 (A), R46.2
unnamed: Q1.3 (B), R7.2, R8.2
unnamed: Q2.3 (B), R44.2
unnamed: Q2.2 (C), R45.2, U6.6
unnamed: R14.2, RV1.1, RV1.2
unnamed: R21.2, U6.1
unnamed: R22.1, U6.2
unnamed: R36.2, R37.1, U8.7
unnamed: R43.2, R44.1, U2.7, U6.5
unnamed: R46.1, U6.3
unnamed: C6.2, R5.2, R6.1, U2.3 (+)
unnamed: U2.2 (-), U9.2 (-), U9.6 (-), U9.13 (-), U9.14
unnamed: R28.2, R29.1, U2.6 (-)
unnamed: C8.1, U3.6 (C1)
unnamed: C8.2, U3.7 (C2)
unnamed: R12.1, U3.13 (PC2)
unnamed: R14.1, U3.11 (R1)
unnamed: R13.1, U3.12 (R2)
unnamed: U3.3 (RefIn), U4.9 (Q)
unnamed: R12.2, U3.9 (VCOin)
unnamed: U4.2 (D), U4.6 (~Q)
unnamed: U4.8 (~Q), U4.12 (D)
unnamed: C11.2, R20.2, U5.3 (+)
unnamed: C10.2, R26.1, U5.1, U5.2 (-)
unnamed: C22.2, R31.2, U5.5 (+)
unnamed: C15.1, C23.2, U5.6 (-), U5.7
unnamed: C13.2, R23.2, U5.10 (+)
unnamed: C14.2, R30.1, U5.8, U5.9 (-)
unnamed: C20.2, R27.2, U5.12 (+)
unnamed: C12.1, C21.2, U5.13 (-), U5.14
unnamed: R42.2, U8.1, U8.3 (+), U8.5 (+), U8.12 (+)
unnamed: C24.1, R32.2, R33.1, U8.2 (-)
unnamed: R34.2, R35.2, R36.1, U8.6 (-)
unnamed: R41.2, R42.1, U8.10 (+)
unnamed: R39.1, R40.2, U8.9 (-)
unnamed: R37.2, R38.1, U8.13 (-)
unnamed: C2.2, R2.1, U9.3 (+)
unnamed: C5.2, R4.1, U9.5 (+)
unnamed: C1.2, R17.2, R18.1, U9.10 (+)
unnamed: R19.1, R21.1, U9.8, U9.9 (-)
unnamed: C18.1, R24.2, R25.1, U9.12 (+)
